dJPoida/watering_system/cad/Hose Clips and Nozzles/Pot Nozzle - Cross Section.png

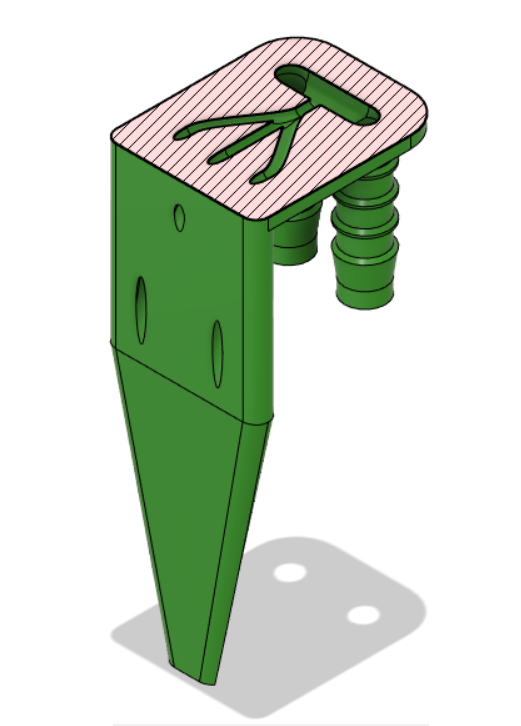
cad/Hose Clips and Nozzles/Pot Nozzle - Cross Section.png
