dJPoida/watering_system/cad/Hose Clips and Nozzles/Pot Nozzle.PNG

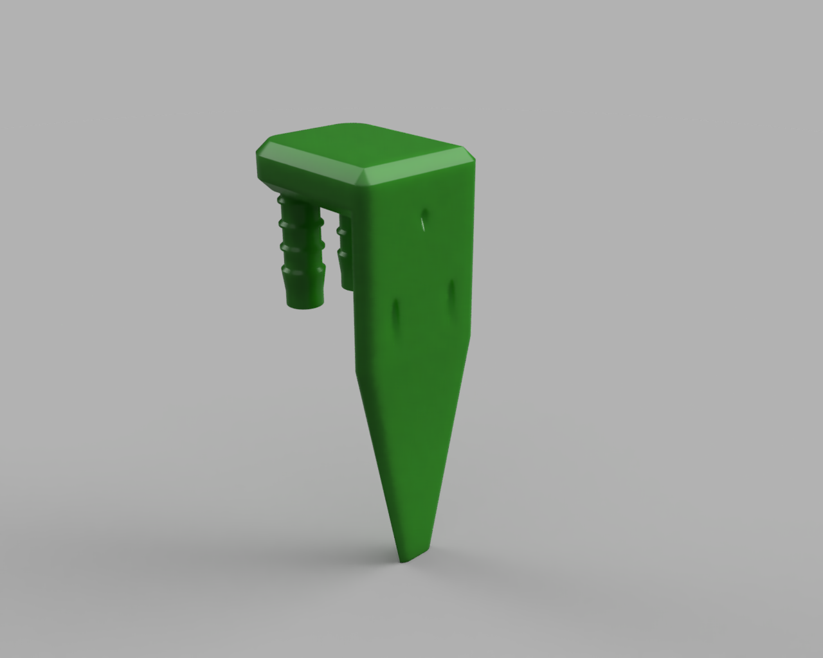
cad/Hose Clips and Nozzles/Pot Nozzle.PNG
